sascha432/trailing_edge_dimmer/docs/images/IMG_8991.JPG

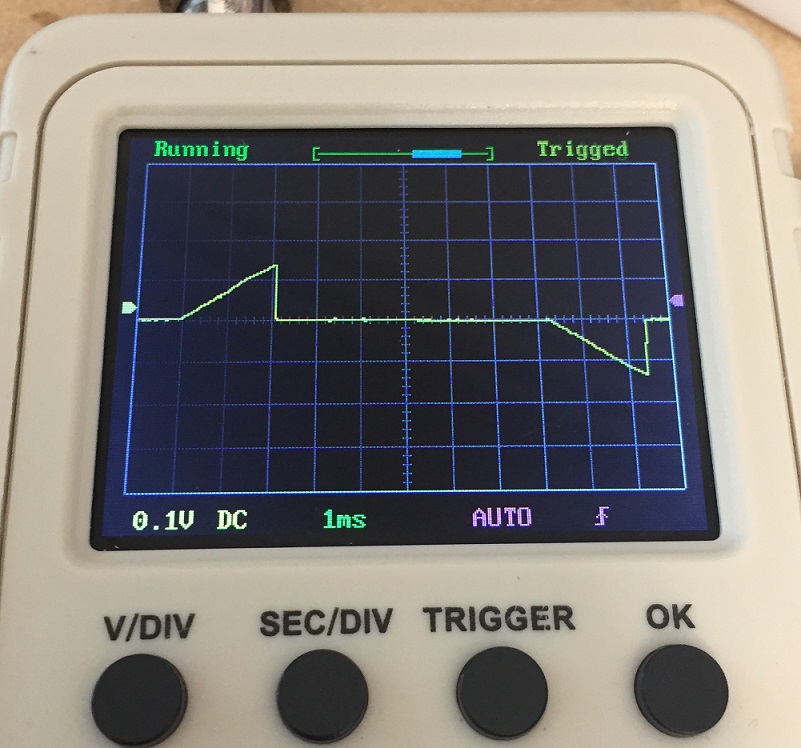
docs/images/IMG_8991.JPG
