sascha432/trailing_edge_dimmer/stl/v1.1/housing_with_power_monitor_rev1.0-1.3/housing_support.stl

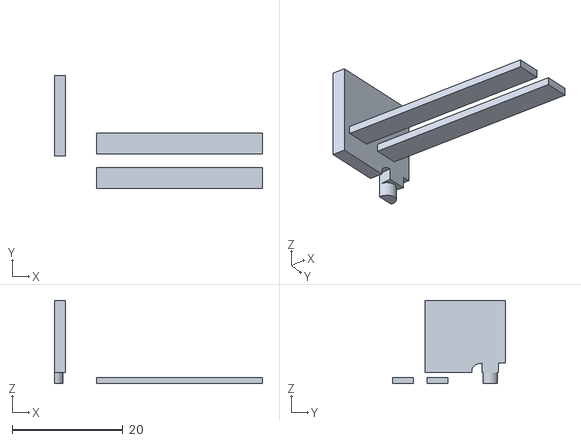
[picture p36: CAD file, 2020-06-01]
stl/v1.1/housing_with_power_monitor_rev1.0-1.3/housing_support.stl
37.6 x 20.4 x 15.0
