sascha432/trailing_edge_dimmer/stl/housing/rocker.stl

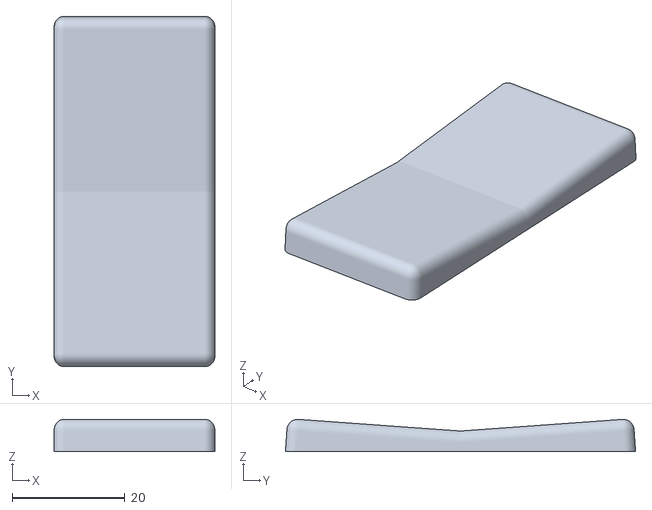
[picture p37: CAD file, 2019-09-30]
stl/housing/rocker.stl
28.5 x 62.0 x 5.72
