sascha432/trailing_edge_dimmer/stl/v1.1/letters_black.stl

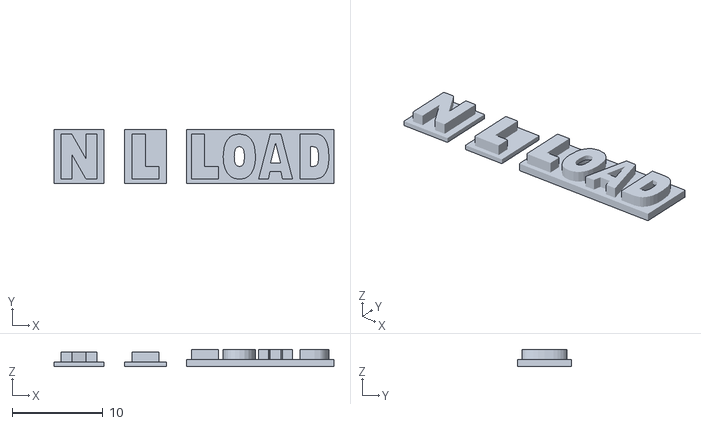
[picture p38: CAD file, 2020-06-01]
stl/v1.1/letters_black.stl
30.9 x 6.00 x 1.90
