sascha432/trailing_edge_dimmer/stl/v1.1/letters_white.stl

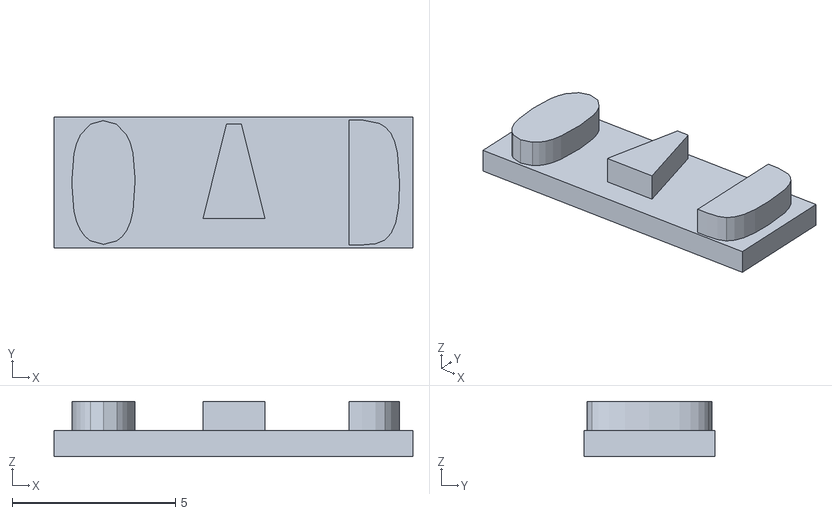
[picture p39: CAD file, 2020-06-01]
stl/v1.1/letters_white.stl
11.0 x 4.00 x 1.70
