sascha432/trailing_edge_dimmer/stl/v1.1/fuse_holder.stl

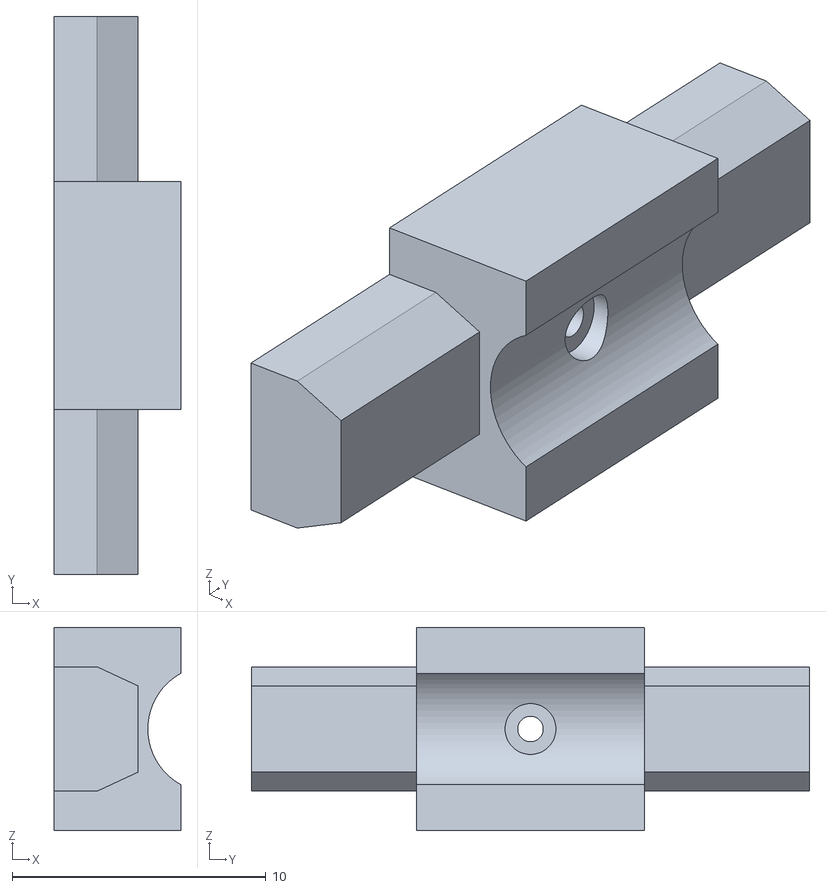
[picture p40: CAD file, 2020-06-01]
stl/v1.1/fuse_holder.stl
5.00 x 22.0 x 8.00
